mprosk/minidrone/sim/eg_ar.asc

C1: cap; 4.7µ
D1: diode
D2: diode
D3: diode
R1: res; 100k
R2: res; 100k
R3: res; 10k
R4: res; 47k
R5: res; 300k
R6: res; 100k
R7: res; 330k
R8: res; 330k
R9: res; 100k
R10: res; 100k
U1: UniversalOpamp2
U2: UniversalOpamp2
U3: UniversalOpamp2
V1: voltage; 12
V2: voltage; 12
V3: voltage; PULSE(0 5 1 1u 1u 15)
Named nets: 0, +12V, -12V, ENV, GATE, TO_VCA, BIAS
.tran 24
